DieSkaarj/Xiyoubu/console.h

#ifndef _CONSOLE_H
#define _CONSOLE_H

#include "enumerations.h"
#include "config.h"

class CPUClock;

class Console
{
    struct Mode
    {
      ELed led;
      ERegion region;
    };

    /*
       Name:  mode
       Desc:  Lookup table for region switching.

    */
    static constexpr Mode mode[4] {
      { SETUP::LED_OFF, INV },
      { SETUP::LED_JAP, JAP },
      { SETUP::LED_EUR, EUR },
      { SETUP::LED_USA, USA }
    };

    static const ERegion load_region();

    void clear_sys_port();
    void clear_led_port();

    void write_sys_port( const byte_t v );
    void write_led_port( const byte_t v );

    void set_sys_region( const ERegion /* Region Code */ );
    void set_led_color( const ELed color );

    void flip_use_controller();
    bool load_controller_preference();

    const ETap tap() { return _tap; }

    int on_tap_timeout( const milliseconds_t /* Ticks */, void( Console::* )() /*Void() Member Function Pointer*/ );

    void cycle_region_timeout( const milliseconds_t /* Ticks */ );
    void cycle_region_reset();
    void can_reconfigure( const bool v ){ _can_reconfigure = v; }
    bool can_tap(){ return _can_tap; }

    void reset_button( const bool t_val ){ _is_button_pressed = t_val; }
    void restart();
    ETap tap( const ETap );

    const ELed led() const;

    static milliseconds_t _chronos, _tap_timer, _cycle_timer;

    static CPUClock _clock;
    static bool _reset_type;
    byte_t _console_region, _tap;
    bool _is_button_pressed,
         _can_reconfigure,
         _can_tap,
         _is_overclocked,
         _lock;

  public:

    bool is_controller_available;

    void on_startup( const milliseconds_t /* Ticks */ );
    void shift_overclock( const bool /* Direction: Up=1/Down=0 */, const bool /* Step size: Big=1/Small=0 */ );
    void check_frequency();
    void in_game_restart();
    void save_region();
    static void poll( const Console*&,const bool /* RESET Button */ );
    void reconfigure( const ERegion t_region=load_region() );
    void handle( const milliseconds_t t_ticks );
    void led_info( ELed t_color1, ELed t_color2 = 0 );

    void check_controller_preference();
    const ERegion region() const;

    Console( const milliseconds_t );
};

#endif//_CONSOLE_H
