DieSkaarj/Xiyoubu/types.h

#ifndef _XIYOUBU_TYPES_H
#define _XIYOUBU_TYPES_H

#include <stdint-gcc.h>

typedef uint16_t pad_combo_t;
typedef uint32_t milliseconds_t;
typedef double frequency_t;
typedef uint8_t byte_t;
typedef uint16_t word_t;
typedef uint32_t big_word_t;
typedef uint8_t port_t;

#endif//_XIYOUBU_TYPES_H
